earabul-sudo/RES-DIC-HD/Drawings/Part Drawings/3dprint_clamps/RLA075_M-Step v1.stl

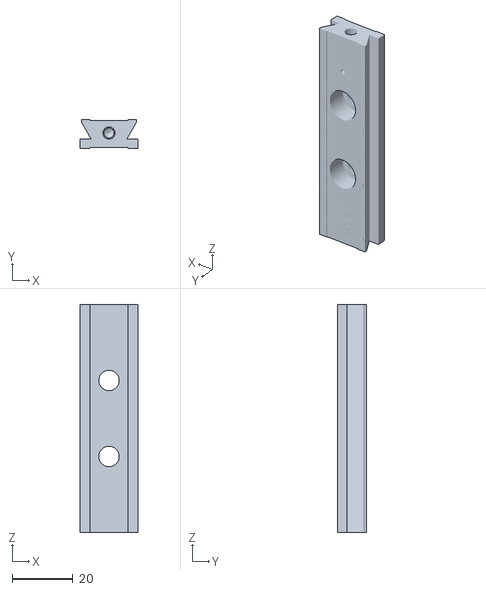
[picture p15: CAD file, 2021-12-12]
Drawings/Part Drawings/3dprint_clamps/RLA075_M-Step v1.stl
19.0 x 9.53 x 75.0
