earabul-sudo/RES-DIC-HD/Drawings/Part Drawings/3dprint_clamps/CL2_M-Step v3.stl

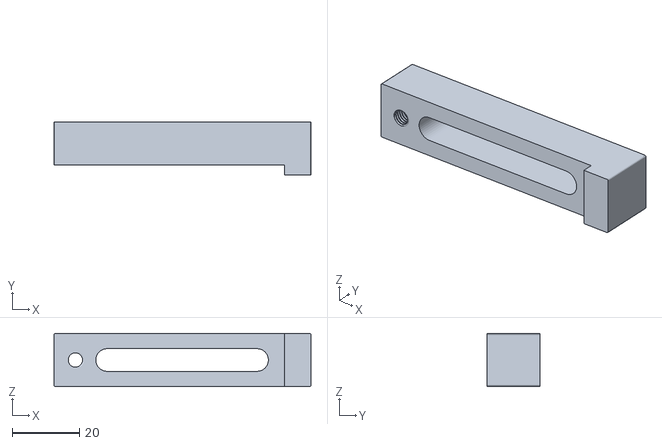
[picture p16: CAD file, 2021-12-12]
Drawings/Part Drawings/3dprint_clamps/CL2_M-Step v3.stl
76.2 x 15.7 x 15.7
