earabul-sudo/RES-DIC-HD/Drawings/Part Drawings/lasercut/20210303_BackWall_EA_00 Drawing v2.pdf

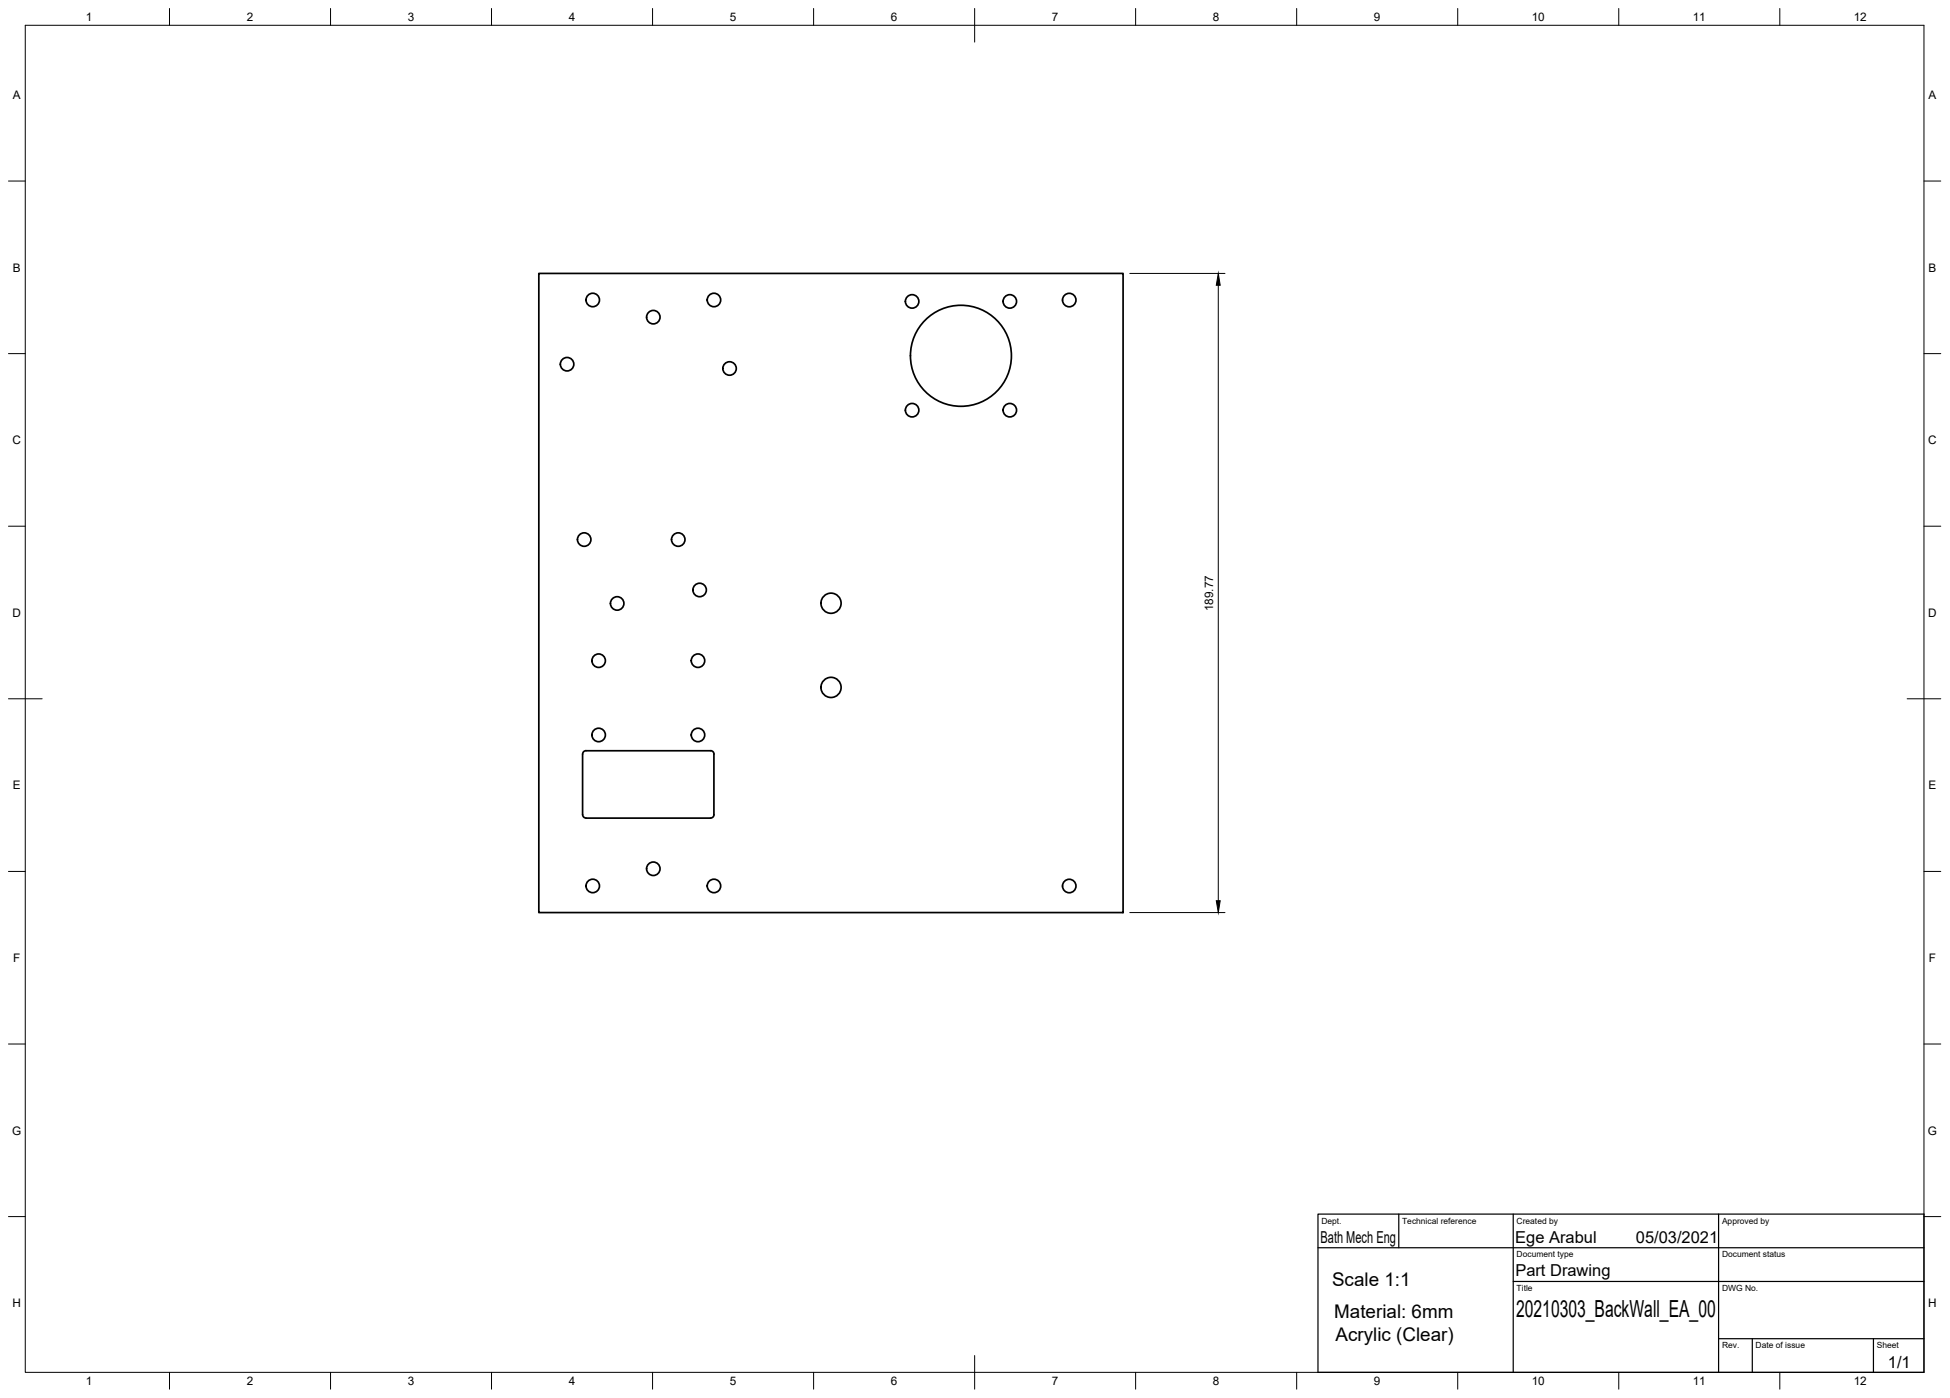
[picture p25: page 1]
Bath Mech Eng; Ege Arabul 189.77

Dept. | Technical reference | Created by 05/03/2021 | Approved by

Scale 1:1 Material: 6mm Acrylic (Clear) | | Document type Part Drawing | Document status

Title 20210303_BackWall_EA_00 | DWG No.

Rev. | Date of issue | Sheet 1/1
