earabul-sudo/RES-DIC-HD/Drawings/Part Drawings/lasercut_2_1to1/20210316_BreadboardBase_Bottom_EA_1to1_00 Drawing v1.pdf

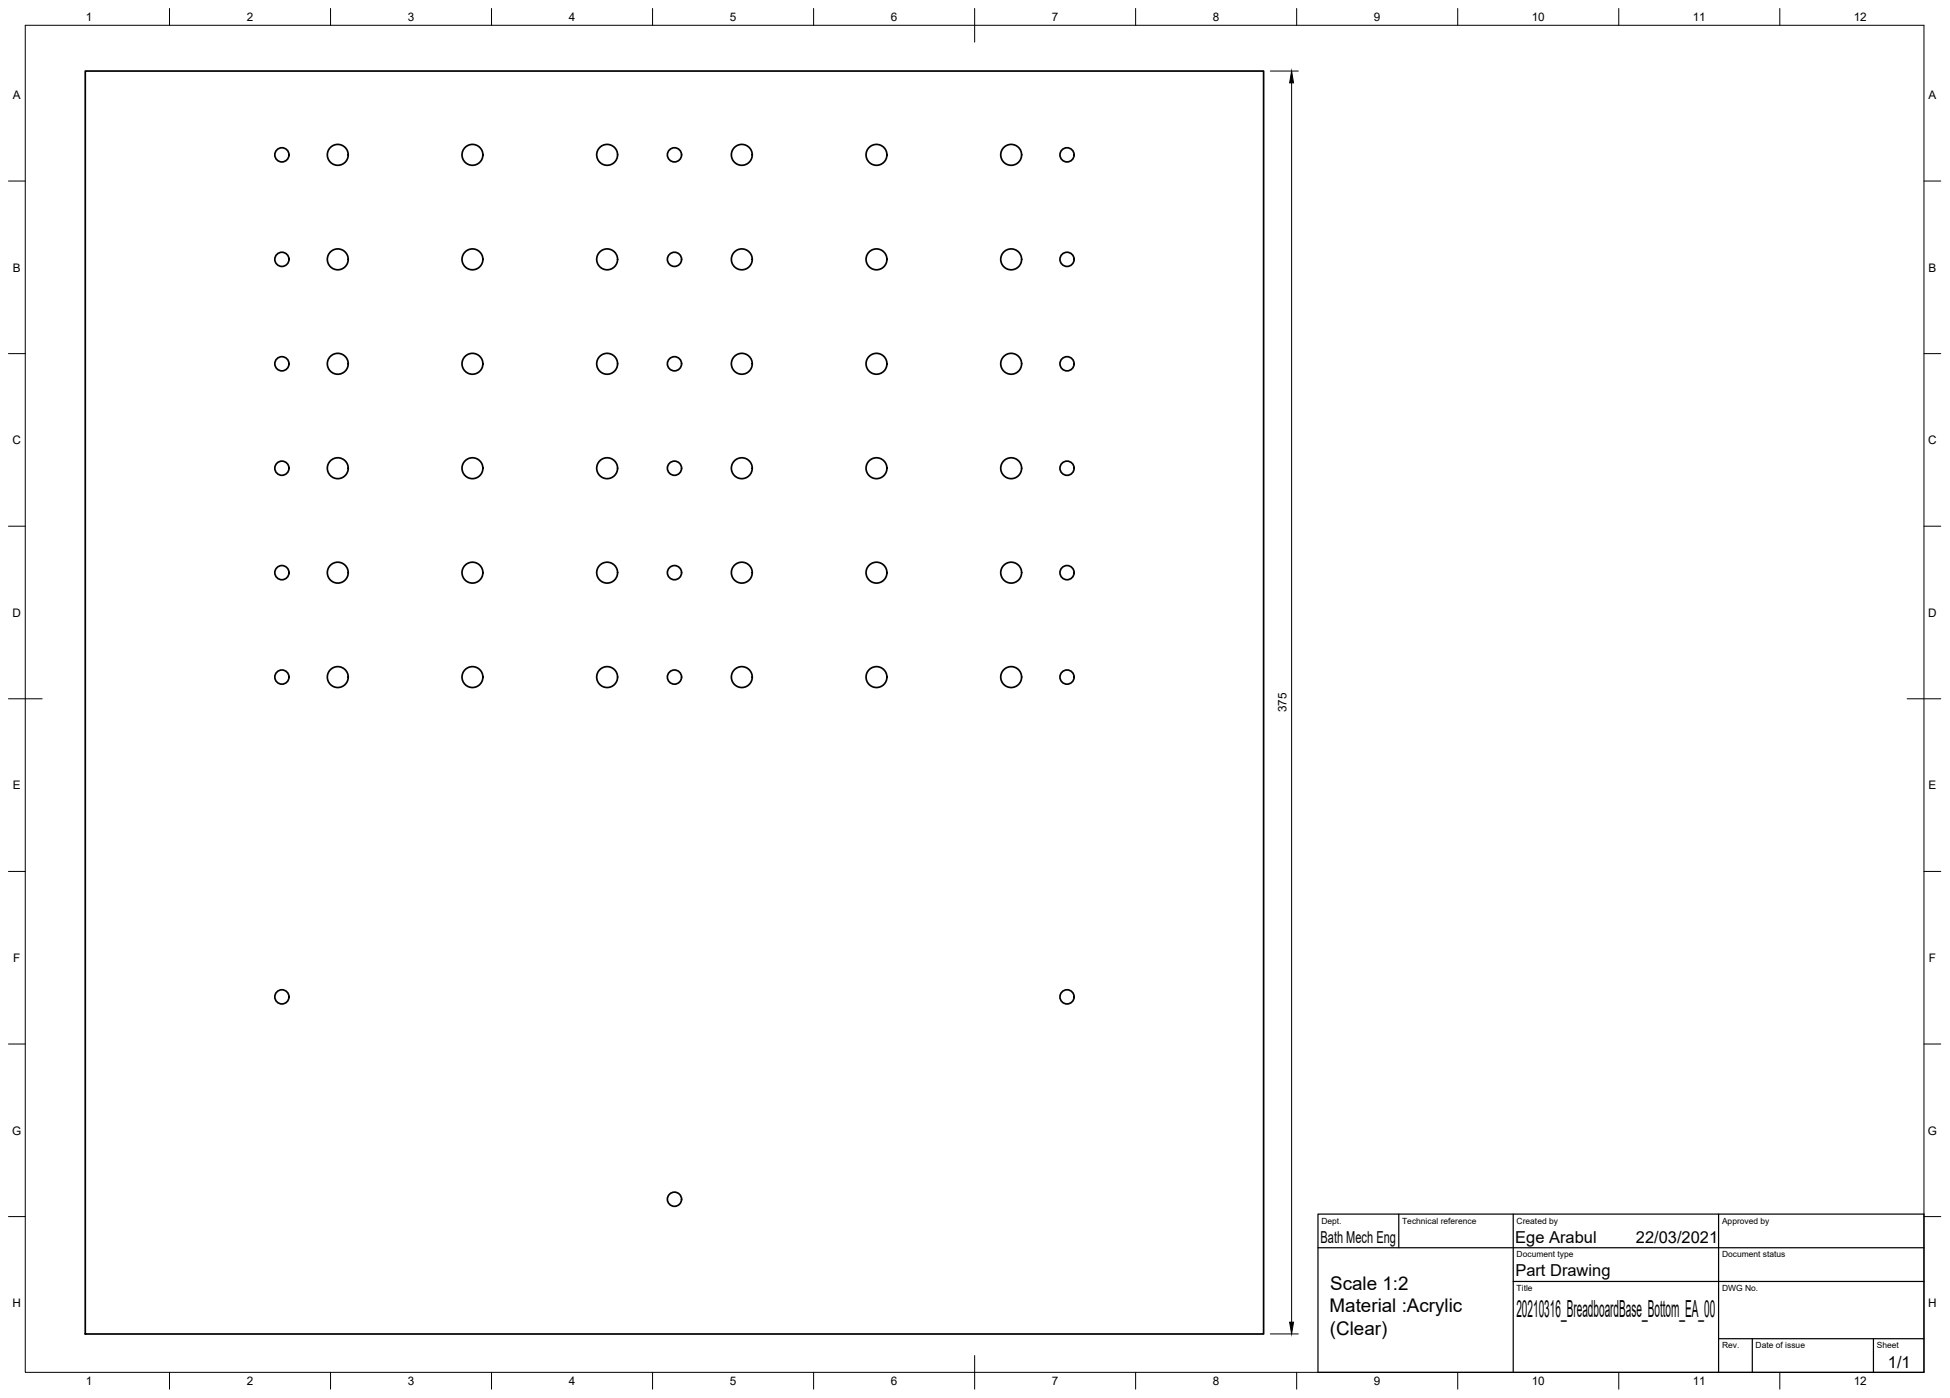
[picture p26: page 1]
Bath Mech Eng; Ege Arabul 375

Dept. | Technical reference | Created by 22/03/2021 | Approved by

Scale 1:2 Material :Acrylic (Clear) | | Document type Part Drawing | Document status

Title 20210316_BreadboardBase_Bottom_EA_00 | DWG No.

Rev. | Date of issue | Sheet 1/1
