earabul-sudo/RES-DIC-HD/Drawings/Part Drawings/machining/20210302_CameraHolder Drawing v16.pdf

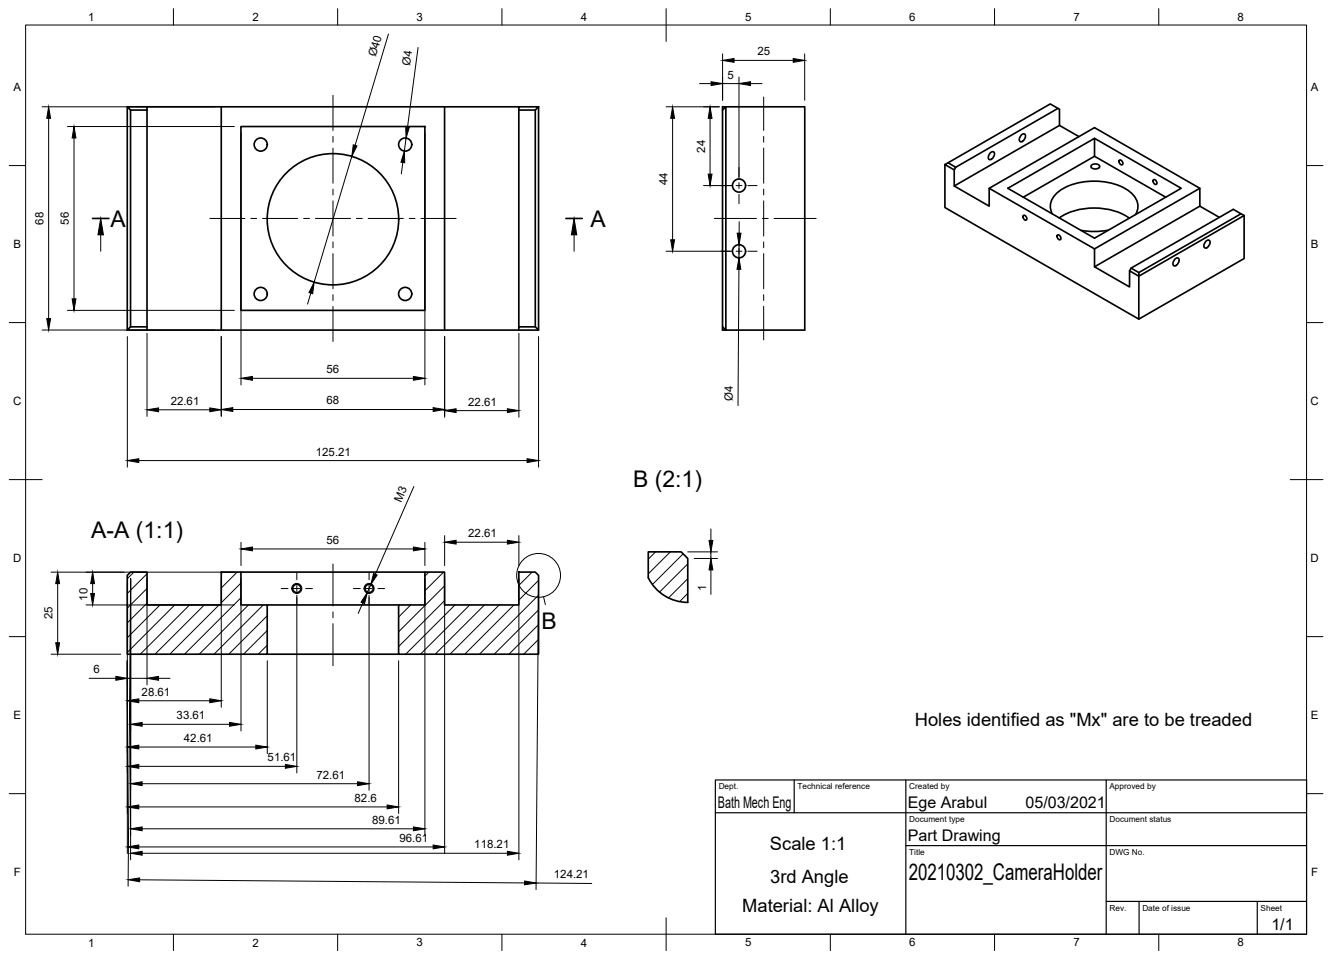
[picture p27: page 1]
Title; DWG No.; Rev.; Date of issue; Sheet; 3rd Angle; Scale 1:1

1 Material: Al Alloy

Holes identified as "Mx" are to be treaded

Dept. Bath Mech Eng | Technical reference | Created by Ege Arabul 05/03/2021 | Approved by

Document type Part Drawing | Document status
