earabul-sudo/RES-DIC-HD/Drawings/Part Drawings/machining/20210305_LeadScrewNut_EA_00 v9.pdf

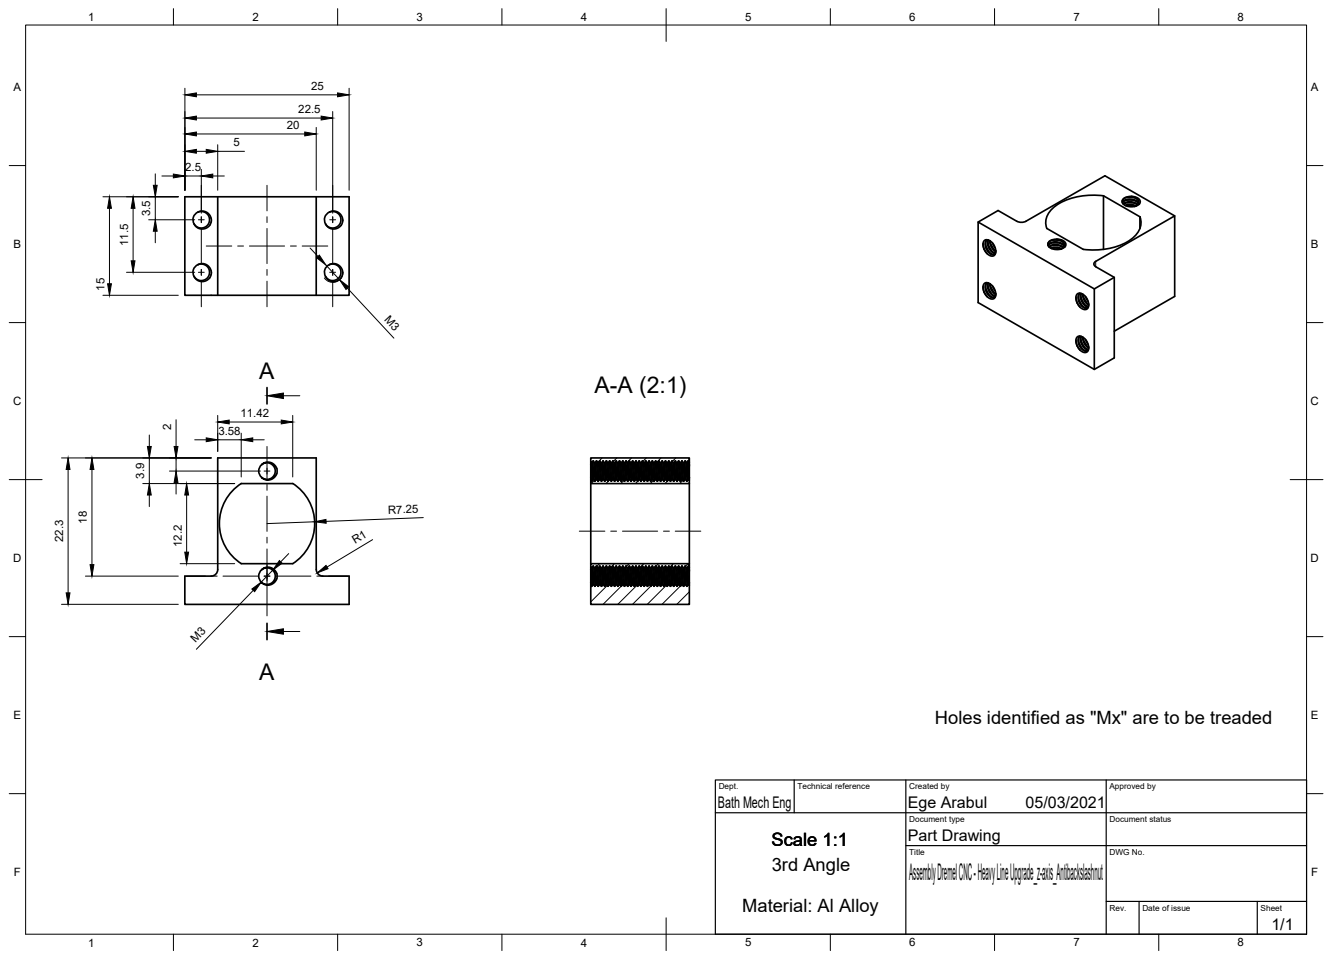
[picture p28: page 1]
Title; DWG No.; Rev.; Date of issue; Sheet; Scale 1:1 3rd Angle

Holes identified as "Mx" are to be treaded

Dept. Bath Mech Eng | Technical reference | Created by Ege Arabul 05/03/2021 | Approved by

Document type Part Drawing | Document status

Assembly Dremel CNC - Heavy Line Upgrade_z-axis_Antibackslashnut

Material: Al Alloy
