earabul-sudo/RES-DIC-HD/Drawings/Part Drawings/machining_2/20210316_BreadboardBase_EA_00 Drawing v10.pdf

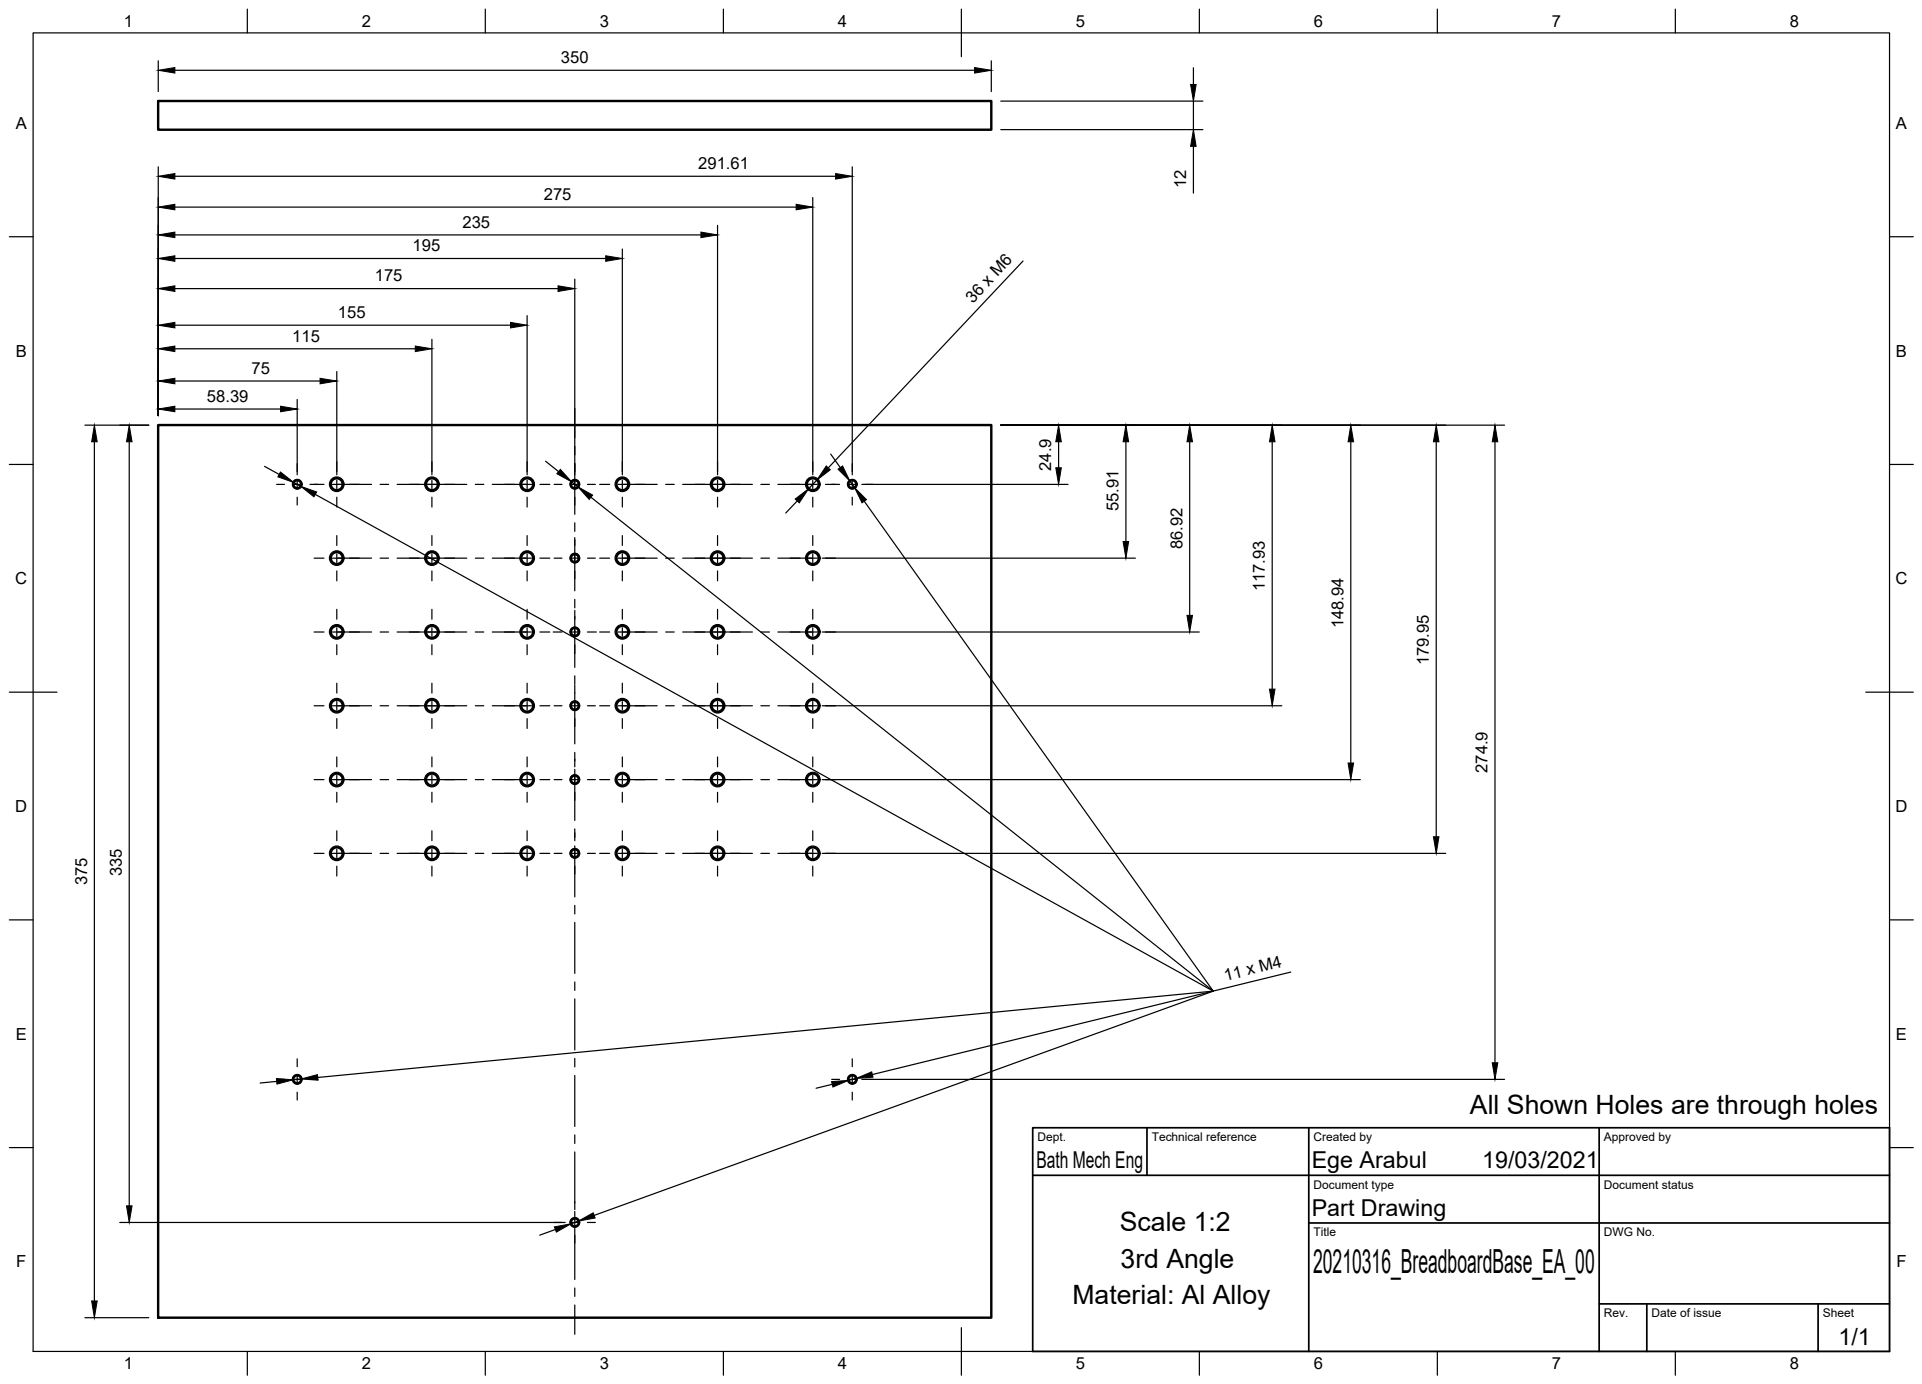
[picture p29: page 1]
Title; DWG No.; Rev.; Date of issue; Sheet; Bath Mech Eng; Ege Arabul 12

All Shown Holes are through holes

Dept. | Technical reference | Created by 19/03/2021 | Approved by

Document type Part Drawing | Document status

Scale 1:2
3rd Angle
Material: Al Alloy
