earabul-sudo/RES-DIC-HD/Drawings/Part Drawings/machining_2/20210317_JawClamp_1Clamp_EA_00 Drawing v8.pdf

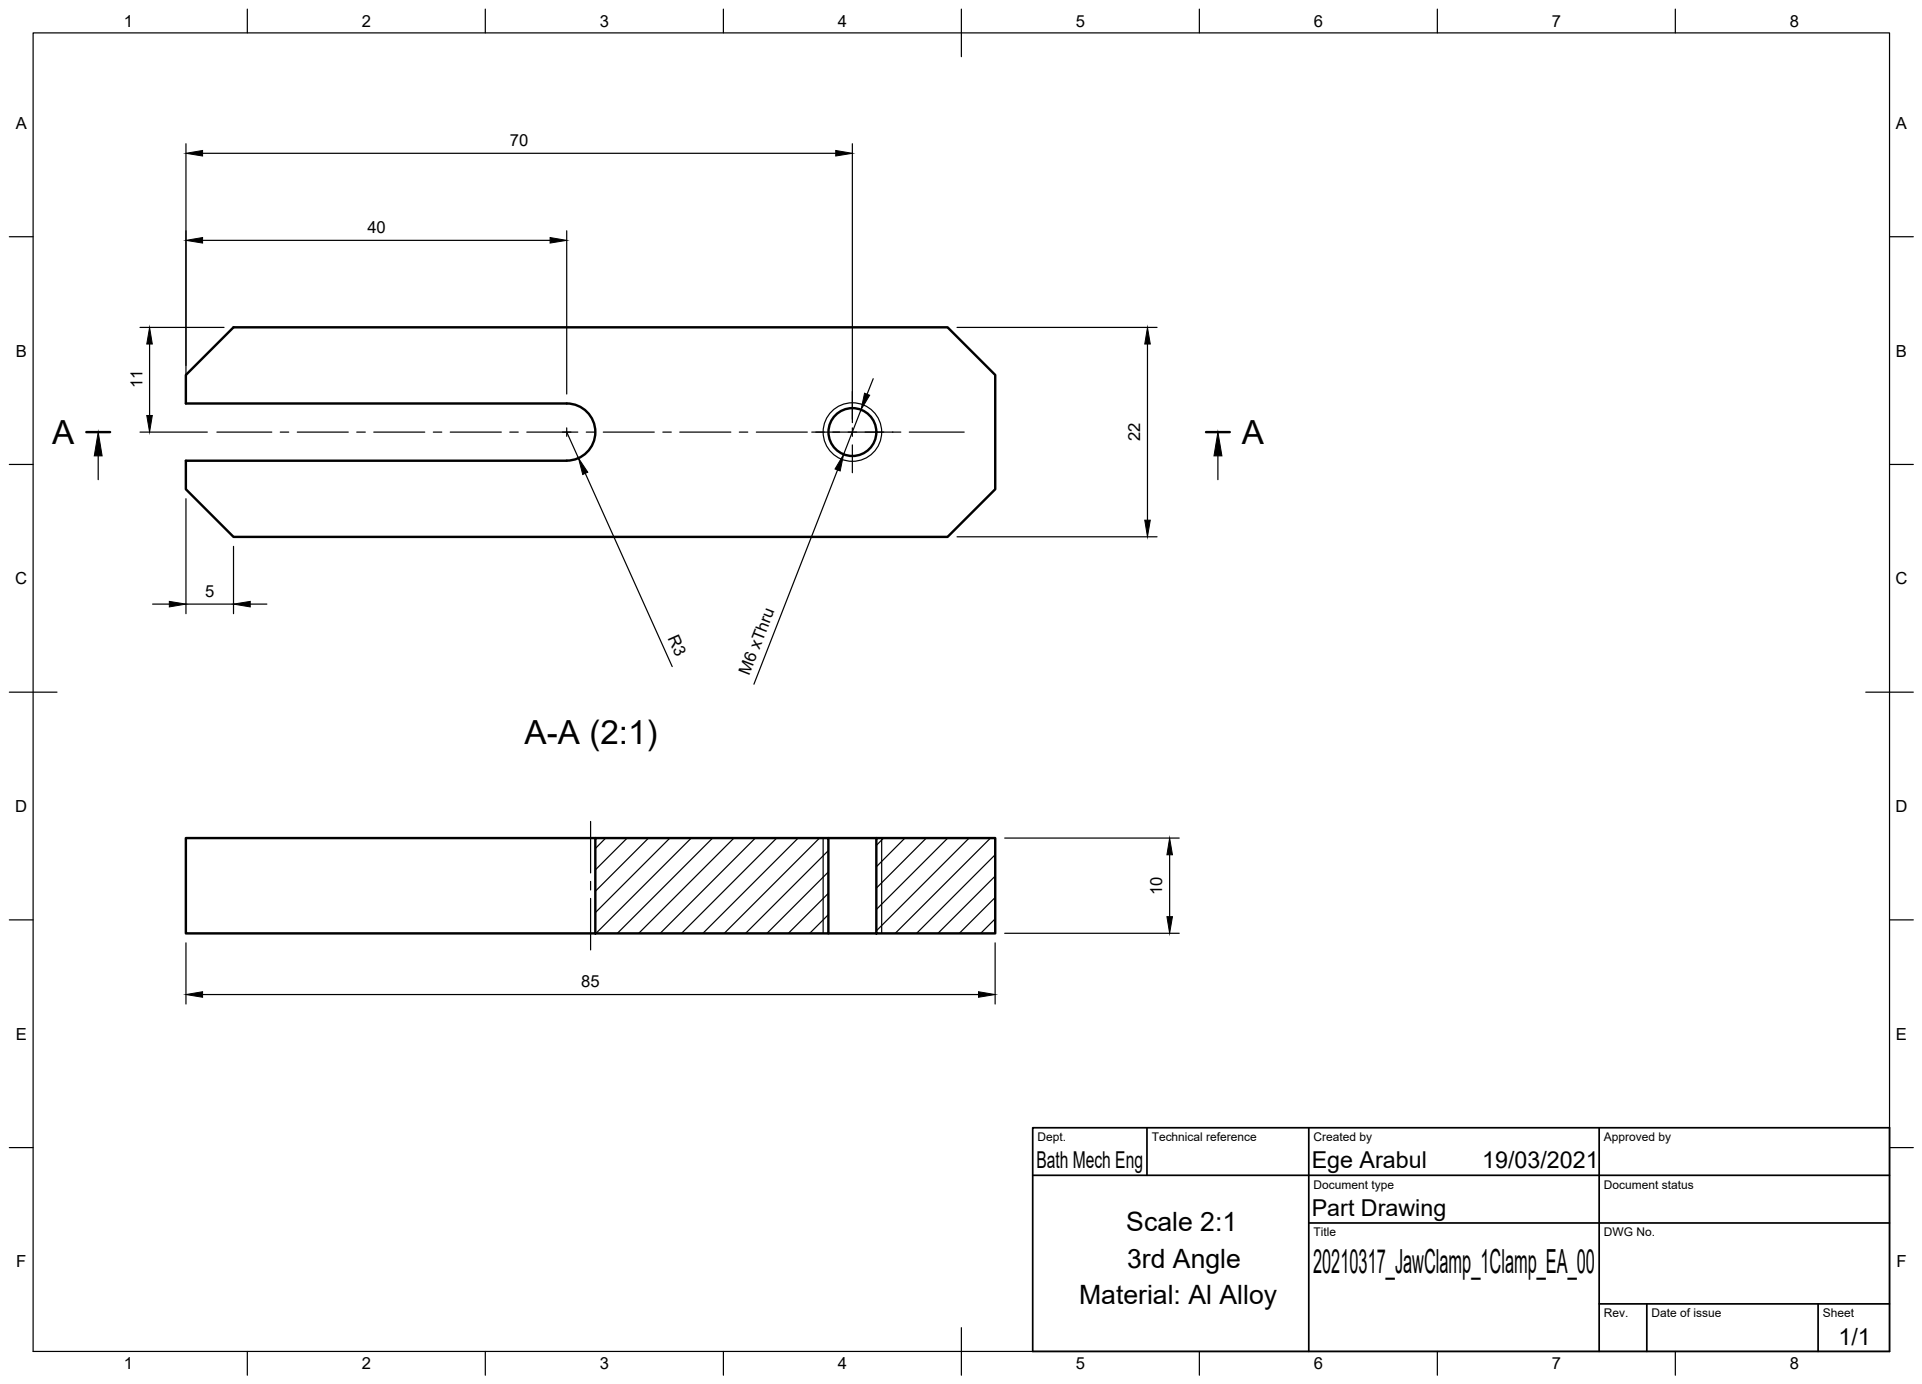
[picture p30: page 1]
Title; DWG No.; Rev.; Date of issue; Sheet; M6 xThru R3 10; Scale 2:1 11

Dept. Bath Mech Eng | Technical reference | Created by Ege Arabul 19/03/2021 | Approved by

Document type Part Drawing | Document status

3rd Angle
Material: Al Alloy
