earabul-sudo/RES-DIC-HD/Drawings/Part Drawings/machining_2/20210317_JawClamp_2Clamps_EA_00 Drawing v7.pdf

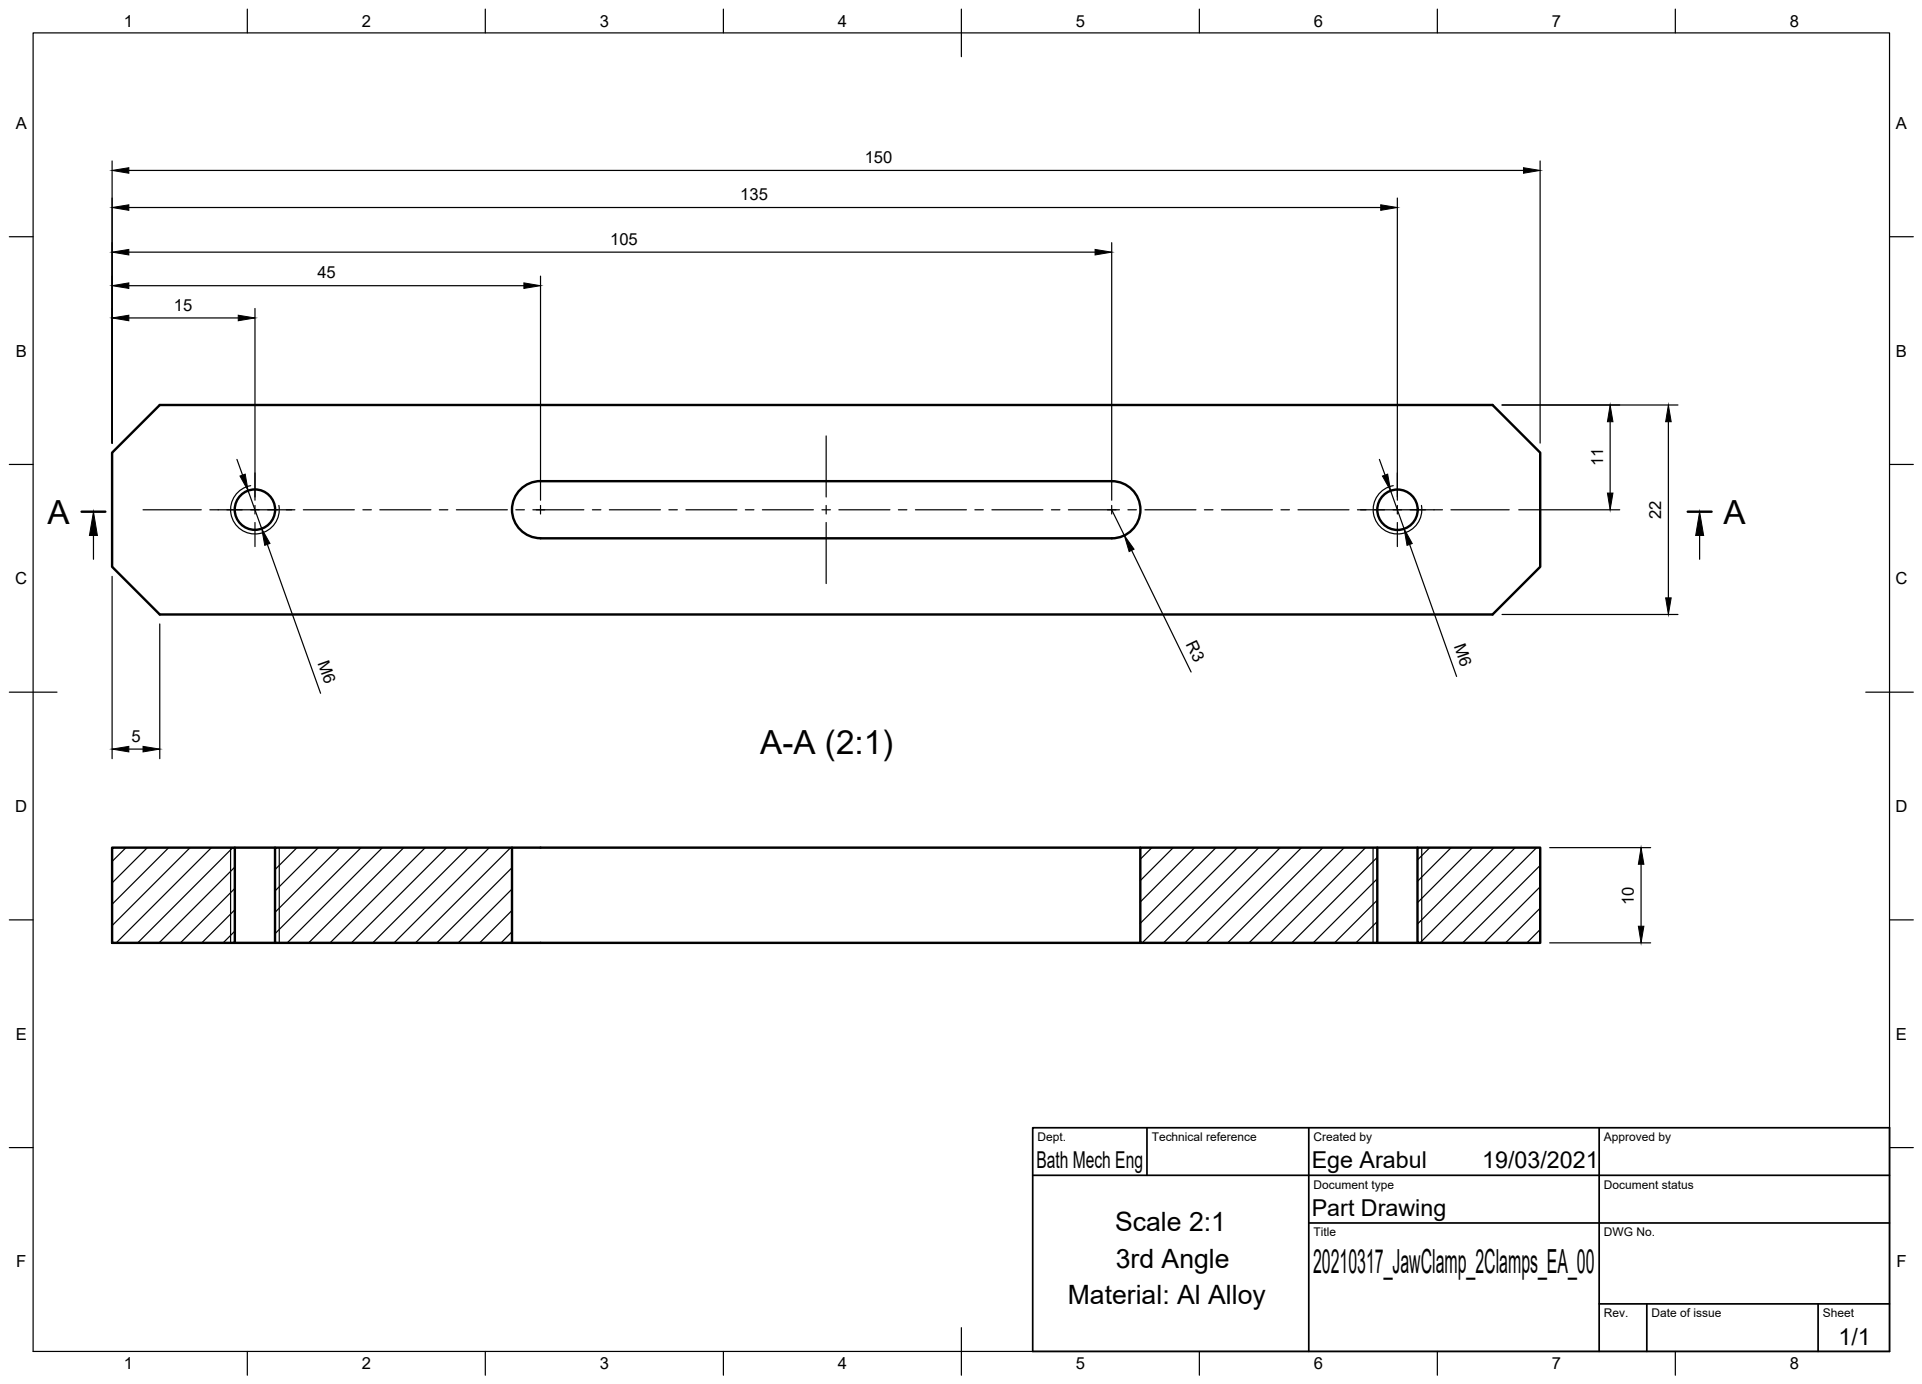
[picture p31: page 1]
Title; DWG No.; Rev.; Date of issue; Sheet

Dept. Bath Mech Eng | Technical reference | Created by Ege Arabul 19/03/2021 | Approved by

Document type Part Drawing | Document status

Scale 2:1
3rd Angle
Material: Al Alloy
