earabul-sudo/RES-DIC-HD/Drawings/Part Drawings/machining_2/20212026_SpacerRods_EA_200mm_00 Drawing v4.pdf

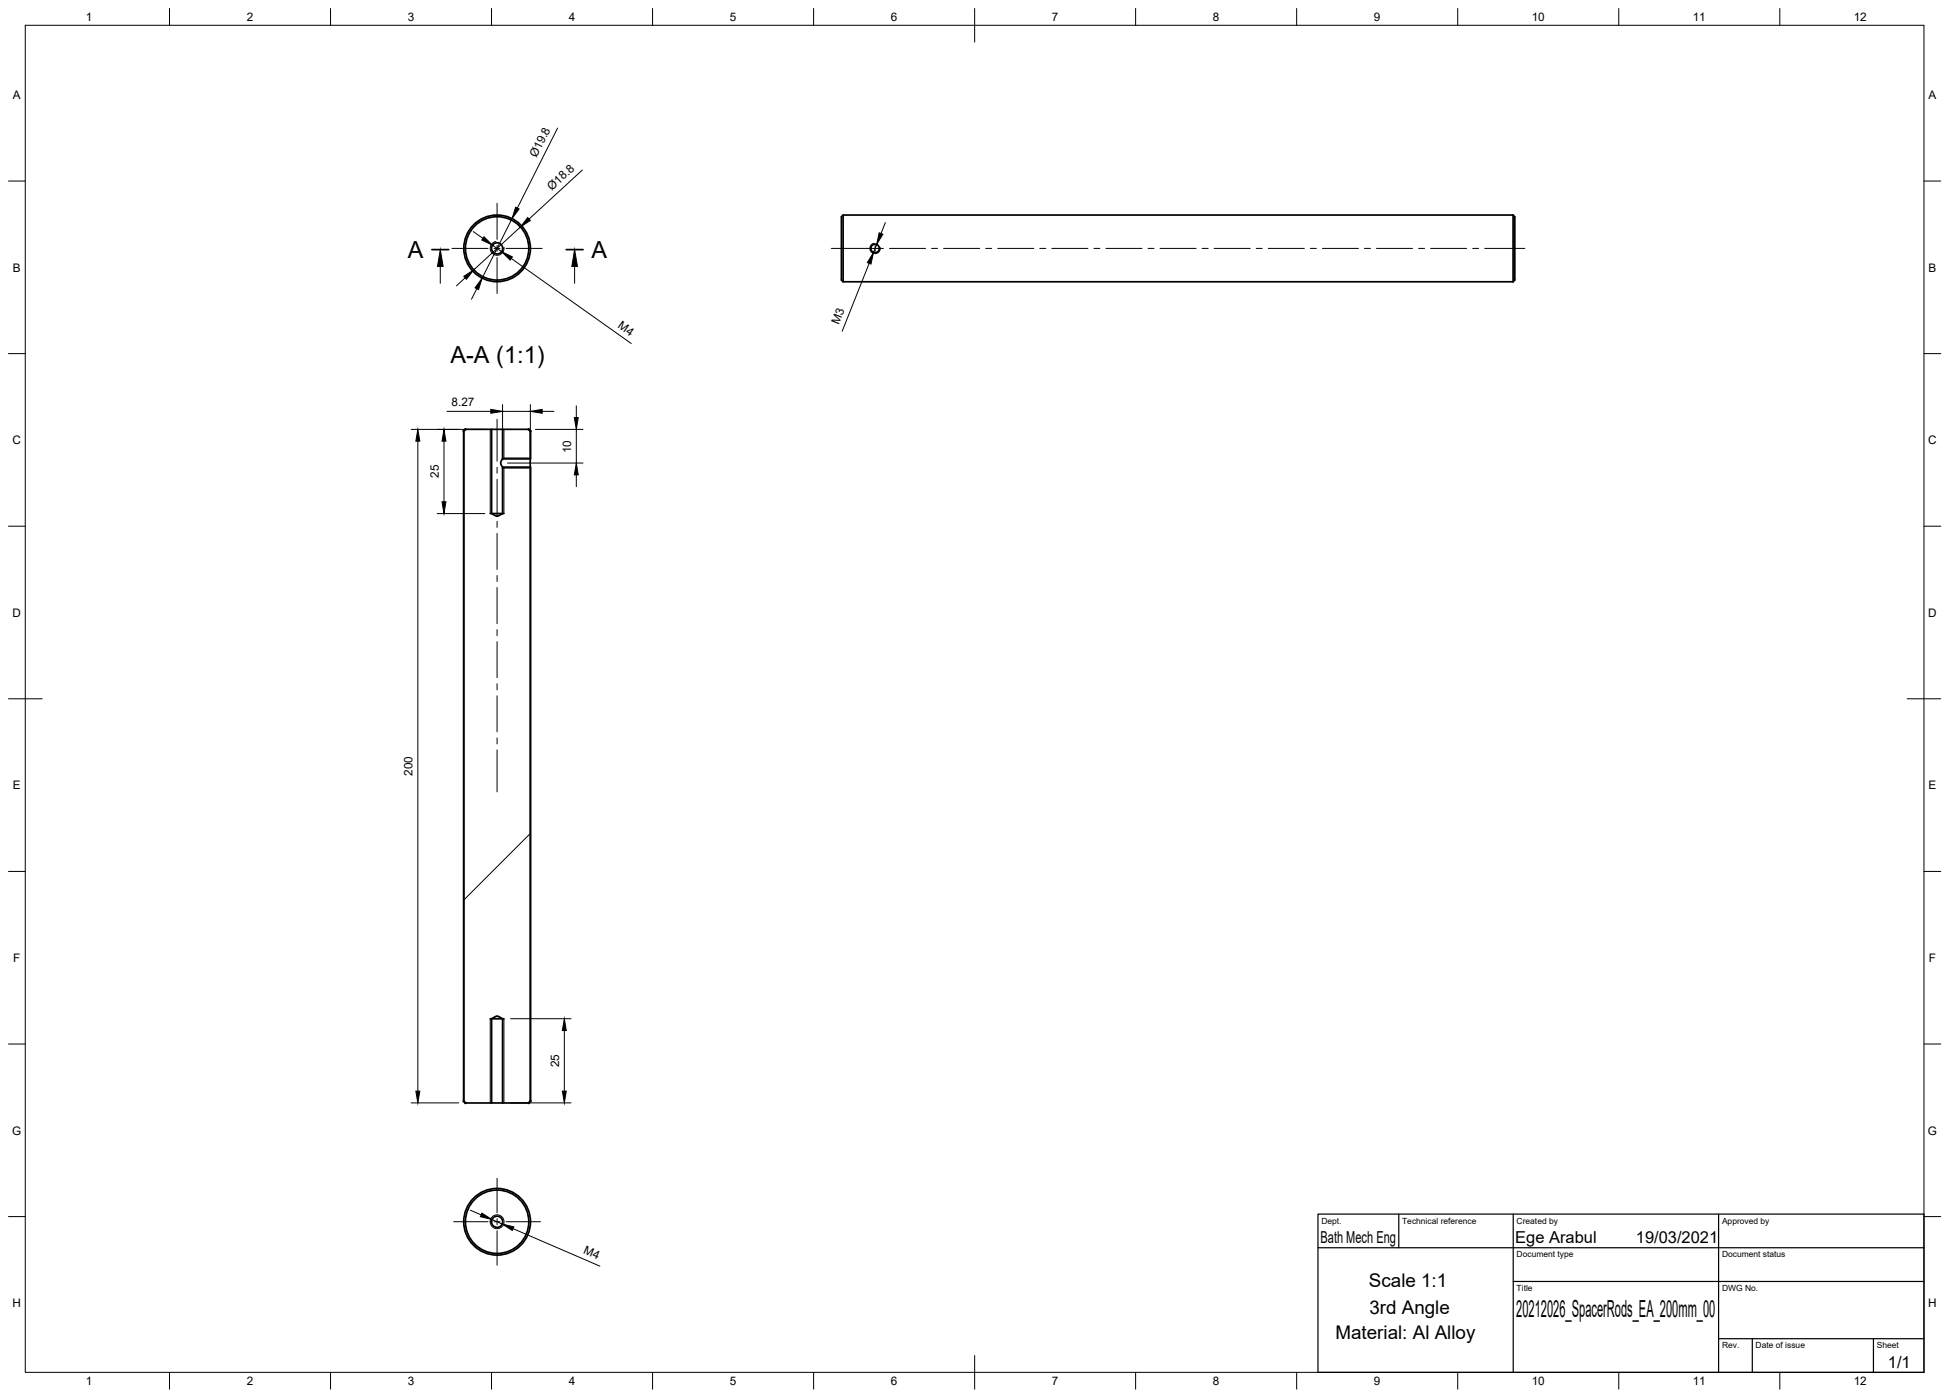
[picture p32: page 1]

Dept. Bath Mech Eng | Technical reference | Created by Ege Arabul 19/03/2021 | Approved by

Scale 1:1 3rd Angle Material: Al Alloy | | Document type | Document status

Title 20212026_SpacerRods_EA_200mm_00 | DWG No.

Rev. | Date of issue | Sheet 1/1
